alexmanuel27/SpectroMatsu/Hardware/3D Comp/vl53l1x-3.snapshot.11/vl531xx/vl53l1x/photo_2025-07-25_13-24-27.jpg

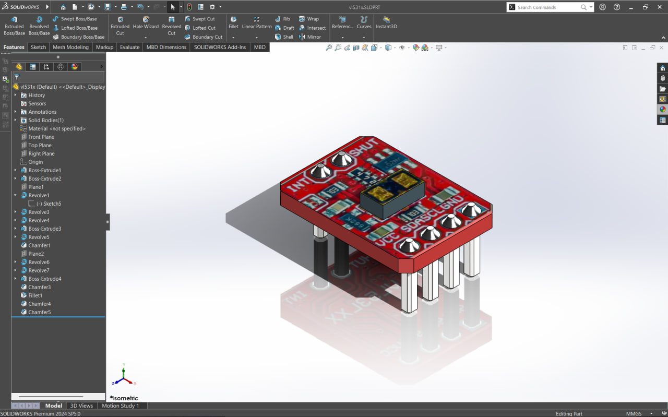
Hardware/3D Comp/vl53l1x-3.snapshot.11/vl531xx/vl53l1x/photo_2025-07-25_13-24-27.jpg
